tinyvision-ai-inc/Vision-FPGA-SoM/SoM/Data/Bringup/IMU_output_shaking.png

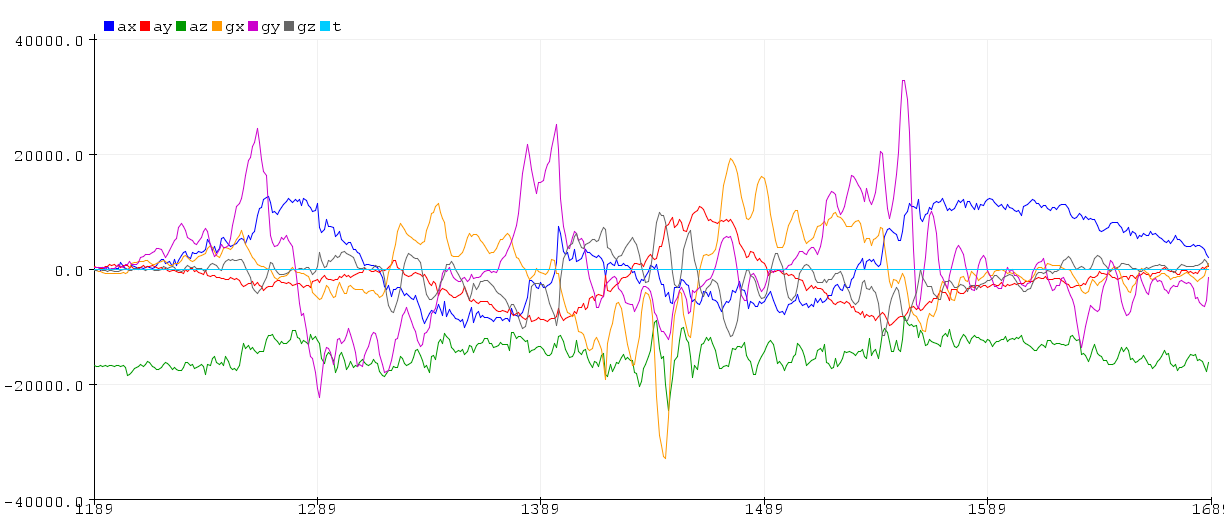
SoM/Data/Bringup/IMU_output_shaking.png
