tinyvision-ai-inc/Vision-FPGA-SoM/SoM/RTL/vision/synth/source/impl_1/dpram512x8/testbench/dut_params.v

localparam FAMILY = "iCE40UP";
localparam MEM_ID = "dpram512x8";
localparam MEM_SIZE = "36,512";
localparam WADDR_DEPTH = 512;
localparam WDATA_WIDTH = 36;
localparam RADDR_DEPTH = 512;
localparam RDATA_WIDTH = 36;
localparam WADDR_WIDTH = 9;
localparam REGMODE = "reg";
localparam RADDR_WIDTH = 9;
localparam OUTPUT_CLK_EN = 0;
localparam RESETMODE = "sync";
localparam BYTE_ENABLE = 0;
localparam BYTE_WIDTH = 1;
localparam BYTE_SIZE = 8;
localparam ECC_ENABLE = 0;
localparam INIT_MODE = "none";
localparam INIT_FILE = "none";
localparam INIT_FILE_FORMAT = "hex";
localparam INIT_VALUE_00 = "0x0000000000000000000000000000000000000000000000000000000000000000";
localparam INIT_VALUE_01 = "0x0000000000000000000000000000000000000000000000000000000000000000";
localparam INIT_VALUE_02 = "0x0000000000000000000000000000000000000000000000000000000000000000";
localparam INIT_VALUE_03 = "0x0000000000000000000000000000000000000000000000000000000000000000";
localparam INIT_VALUE_04 = "0x0000000000000000000000000000000000000000000000000000000000000000";
localparam INIT_VALUE_05 = "0x0000000000000000000000000000000000000000000000000000000000000000";
localparam INIT_VALUE_06 = "0x0000000000000000000000000000000000000000000000000000000000000000";
localparam INIT_VALUE_07 = "0x0000000000000000000000000000000000000000000000000000000000000000";
localparam INIT_VALUE_08 = "0x0000000000000000000000000000000000000000000000000000000000000000";
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
localparam INIT_VALUE_34 = "0x0000000000000000000000000000000000000000000000000000000000000000";
localparam INIT_VALUE_35 = "0x0000000000000000000000000000000000000000000000000000000000000000";
localparam INIT_VALUE_36 = "0x0000000000000000000000000000000000000000000000000000000000000000";
localparam INIT_VALUE_37 = "0x0000000000000000000000000000000000000000000000000000000000000000";
localparam INIT_VALUE_38 = "0x0000000000000000000000000000000000000000000000000000000000000000";
localparam INIT_VALUE_39 = "0x0000000000000000000000000000000000000000000000000000000000000000";
localparam INIT_VALUE_3A = "0x0000000000000000000000000000000000000000000000000000000000000000";
localparam INIT_VALUE_3B = "0x0000000000000000000000000000000000000000000000000000000000000000";
localparam INIT_VALUE_3C = "0x0000000000000000000000000000000000000000000000000000000000000000";
localparam INIT_VALUE_3D = "0x0000000000000000000000000000000000000000000000000000000000000000";
localparam INIT_VALUE_3E = "0x0000000000000000000000000000000000000000000000000000000000000000";
localparam INIT_VALUE_3F = "0x0000000000000000000000000000000000000000000000000000000000000000";
`define ICE40UP
