tinyvision-ai-inc/Vision-FPGA-SoM/SoM/RTL/vision/synth/source/impl_1/dpram512x8/misc/dpram512x8_tmpl.vhd

component dpram512x8 is
    port(
        wr_clk_i: in std_logic;
        rd_clk_i: in std_logic;
        rst_i: in std_logic;
        wr_clk_en_i: in std_logic;
        rd_en_i: in std_logic;
        rd_clk_en_i: in std_logic;
        wr_en_i: in std_logic;
        wr_data_i: in std_logic_vector(35 downto 0);
        wr_addr_i: in std_logic_vector(8 downto 0);
        rd_addr_i: in std_logic_vector(8 downto 0);
        rd_data_o: out std_logic_vector(35 downto 0)
    );
end component;

__: dpram512x8 port map(
    wr_clk_i=>,
    rd_clk_i=>,
    rst_i=>,
    wr_clk_en_i=>,
    rd_en_i=>,
    rd_clk_en_i=>,
    wr_en_i=>,
    wr_data_i=>,
    wr_addr_i=>,
    rd_addr_i=>,
    rd_data_o=>
);
